Fju/NanoStation/src/nanostation.h

#ifndef NANOSTATION_H
#define NANOSTATION_H


#define PIN_STICK_X         A1
#define PIN_STICK_Y         A2
#define PIN_STICK_BUTTON    5
#define PIN_BUTTON_A        11
#define PIN_BUTTON_B        12

#define COLOR_WHITE   3
#define COLOR_BLUE    2
#define COLOR_YELLOW  1
#define COLOR_BLACK   0


#define SCREEN_WIDTH  120
#define SCREEN_HEIGHT 60


#endif /* NANOSTATION_H */
