Fju/NanoStation/src/up2/screen.h

#ifndef SCREEN_H
#define SCREEN_H

#include <VGAX.h>
#include "nanostation.h"
#include "platform.h"

void screen(char * line1, char * line2);

void level_screen();

void win_screen();

void clear_screen();

void draw_platforms(Platform * platforms, byte platform_amount, byte time);

void force_draw_platforms(Platform * platforms, byte platform_amount, byte time);

#endif /* SCREEN_H */
